ABillBlakely/Firemace-distortion-pedal/solidworks-firemace/guitar input jack/InputJack2.jpg

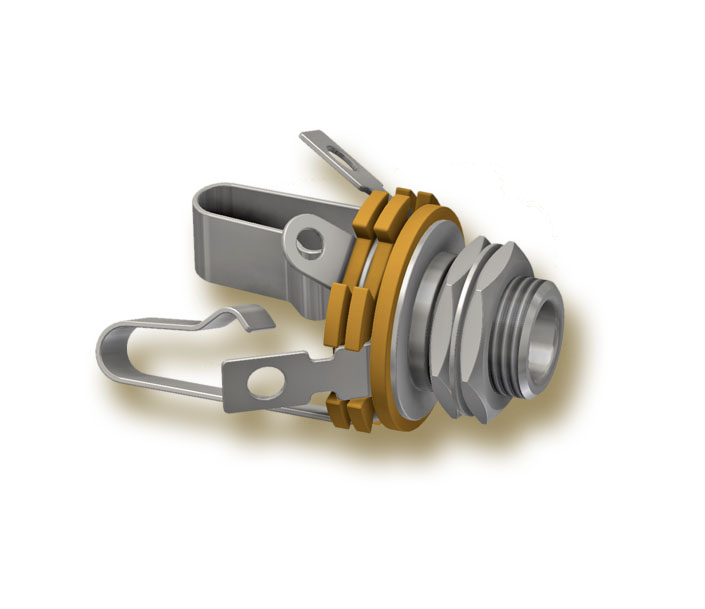
solidworks-firemace/guitar input jack/InputJack2.jpg
