ABillBlakely/Firemace-distortion-pedal/modifications/diode options.asc

D1: diode; 1N4007
D2: diode; 1N4007
D3: diode; 1N4148
D4: diode; 1N4148
D5: diode; 1N4148
D6: diode; 1N4148
D7: diode; 1N4148
D8: LED; Blue
D9: LED; Red
D10: diode; 1N4148
D11: diode; 1N4148
Standard Conn.
Different Diode.
Silicon at larger voltage
Slightly Assymetric
Very Assymetric
