ABillBlakely/Firemace-distortion-pedal/modifications/opamp options.asc

C1: cap; 1µ
C2: cap; 1µ
C3: cap; 10µ
R1: res; 10k
R2: res; 10k
R3: res; 100k
R4: res; 100k
RV3A: res; 500k
RV3B: res; 500k
U1A: opamp
V1: voltage; 9
Named nets: Dirty_signal, 0, Dry_signal, +9V, Output
Blend pot replace volume
Summing Amp
.lib opamp.sub
.tran 2m
Additional volume pot could be added here.
