ABillBlakely/Firemace-distortion-pedal/modifications/slew rate.asc

C1: cap; 1µ
R1: res; 1.01Meg
R2: res; 1.8k
U1: UniversalOpamp2; Avol=1Meg GBW=10Meg Slew=1Meg
V1: voltage; SINE(100 0.1 {freq})
V2: voltage; 200
Named nets: 0, Vcc
.step param freq list 1k 10k
.tran 0 2m 1m
.lib opamp.sub
